madmaxom/SAN_Project/images/IMG_20180602_152641.jpg

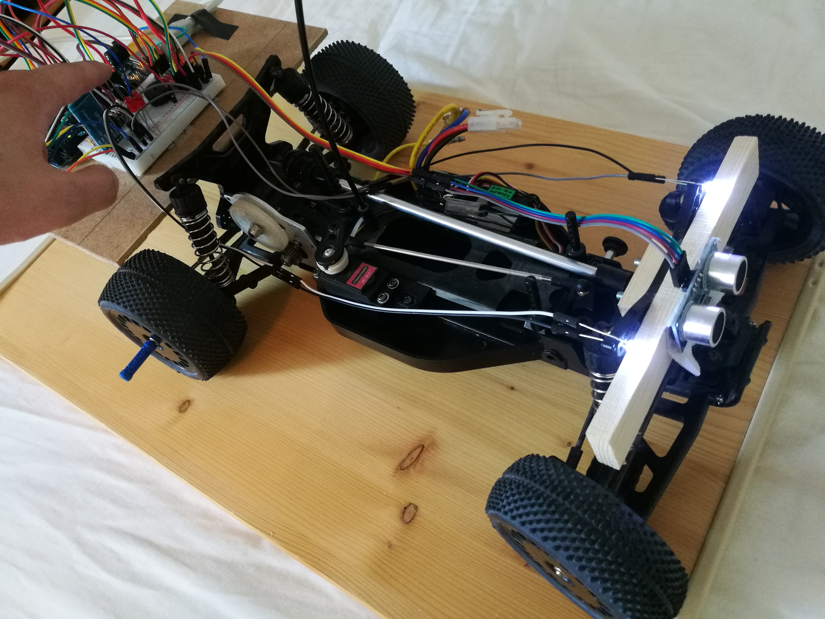
images/IMG_20180602_152641.jpg
