madmaxom/SAN_Project/images/IMG_20180602_152652.jpg

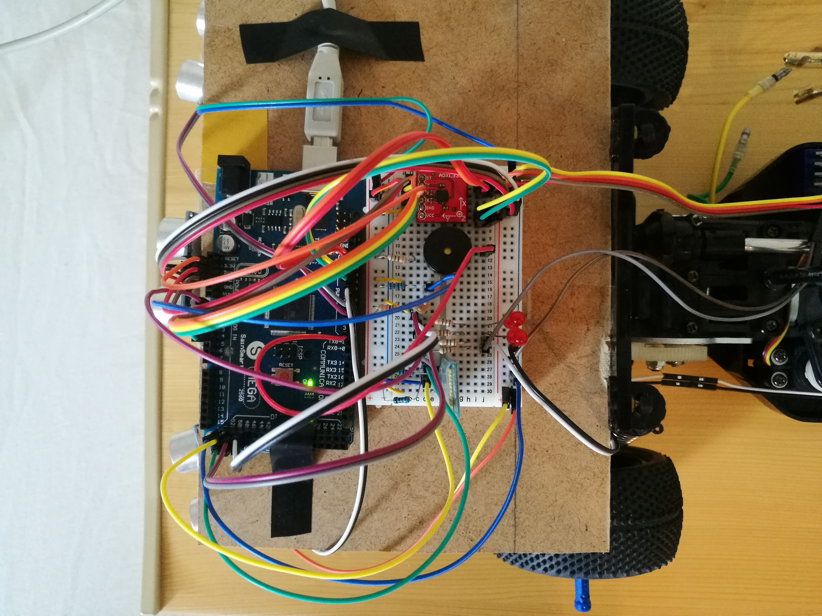
images/IMG_20180602_152652.jpg
